tanaka-su951/mtk64ebt/image/fooswitch_bt_module.png

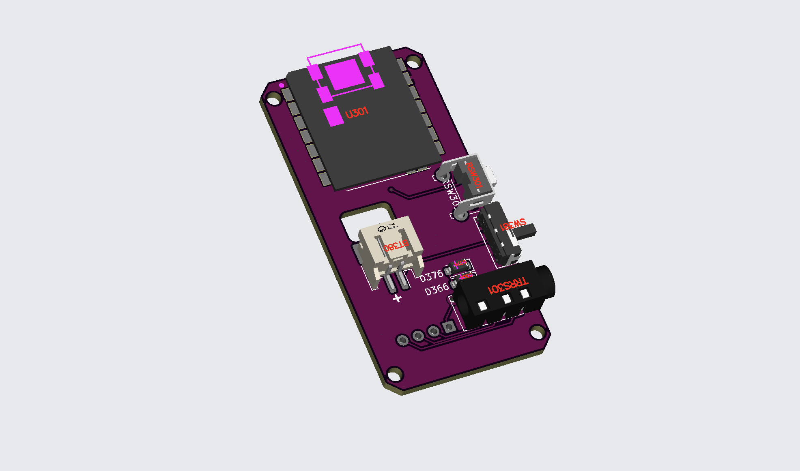
image/fooswitch_bt_module.png
