tanaka-su951/mtk64ebt/image/footmodule_gerber.png

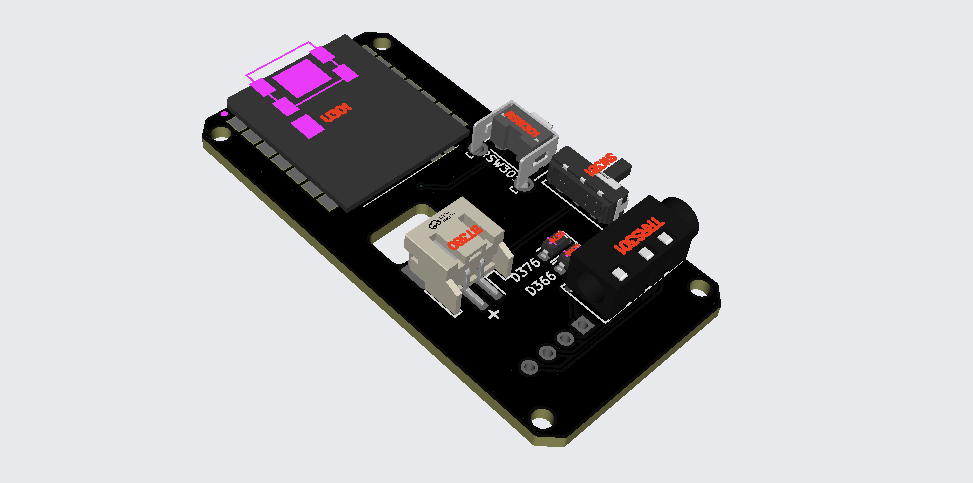
image/footmodule_gerber.png
