tanaka-su951/mtk64ebt/image/mtk64ebt_case.jpg

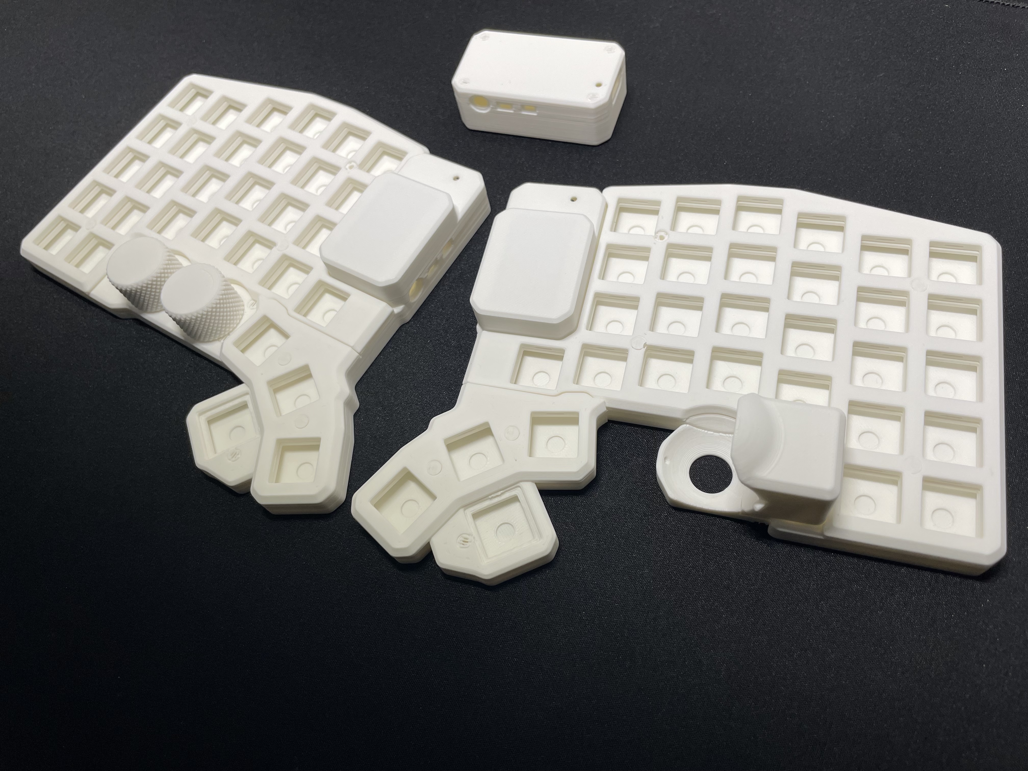
image/mtk64ebt_case.jpg
