tanaka-su951/mtk64ebt/image/mtk64ebt_L2.jpg

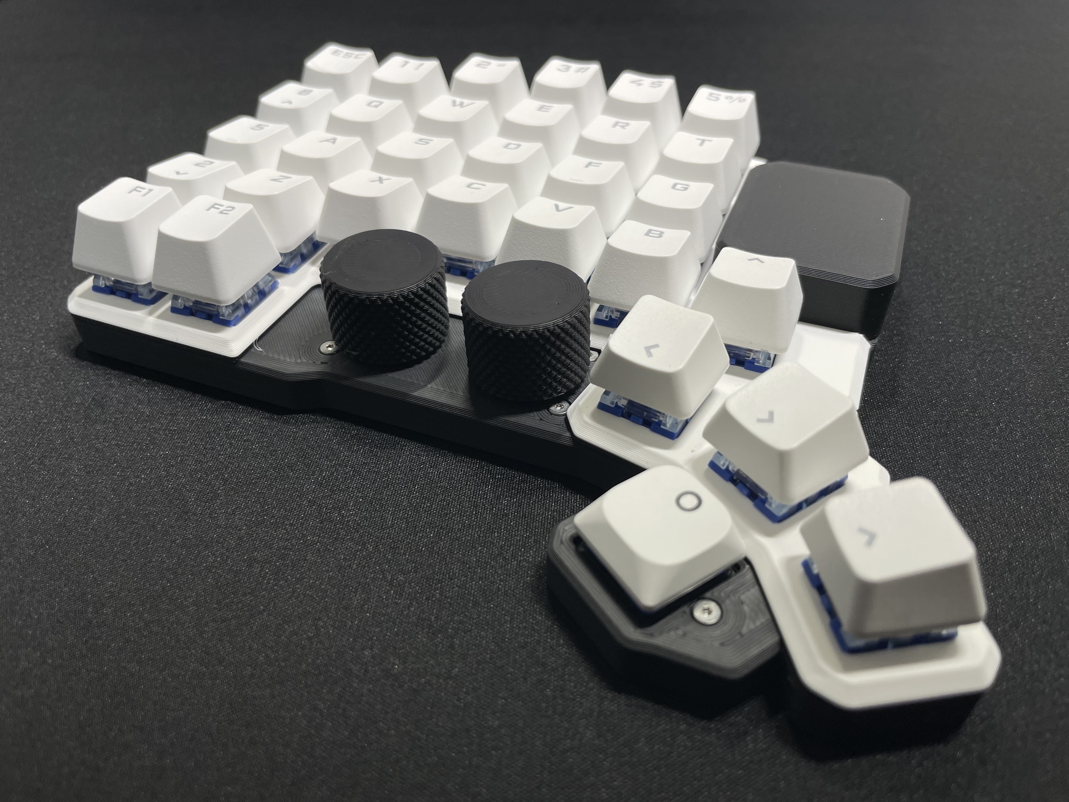
image/mtk64ebt_L2.jpg
