tanaka-su951/mtk64ebt/image/mtk64ebt_L.jpg

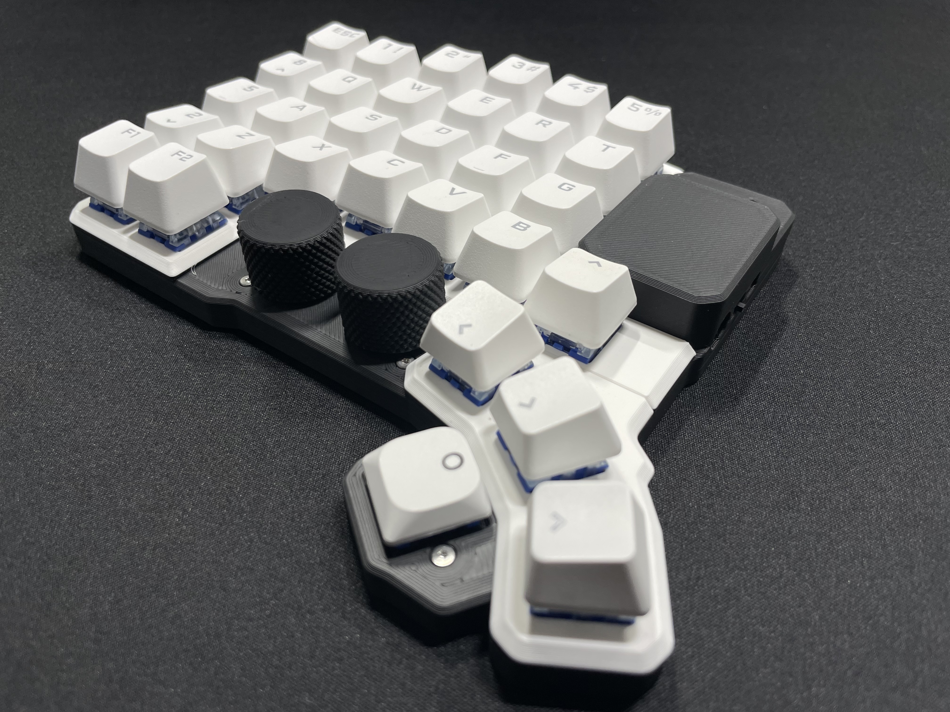
image/mtk64ebt_L.jpg
