tanaka-su951/mtk64ebt/image/mtk64ebt_lowpro.jpg

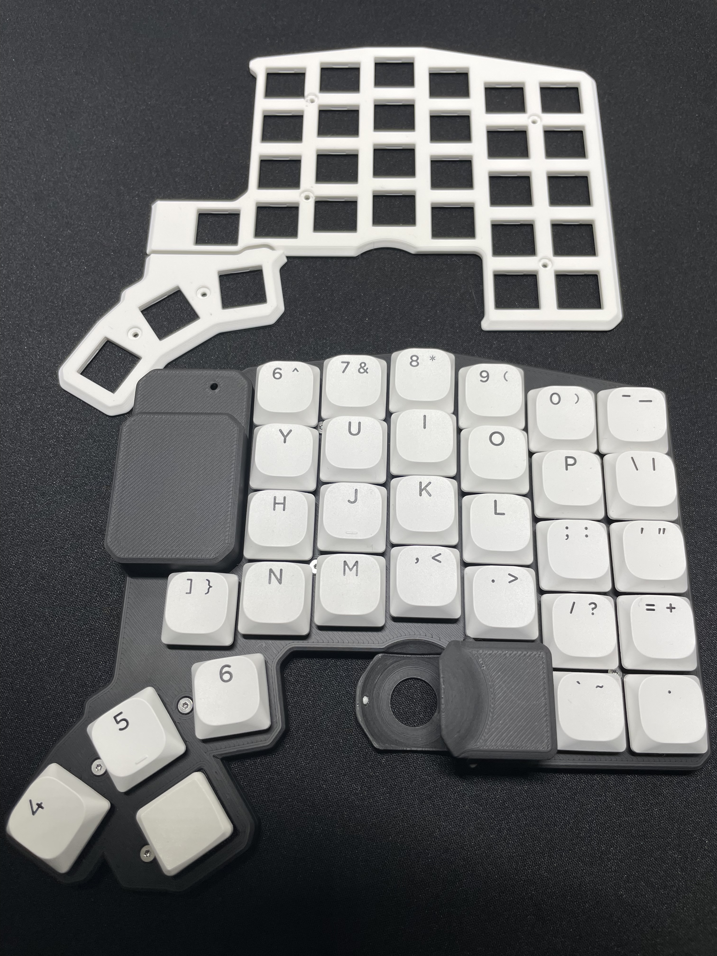
image/mtk64ebt_lowpro.jpg
