tanaka-su951/mtk64ebt/image/mtk64ebt_prototype.JPG

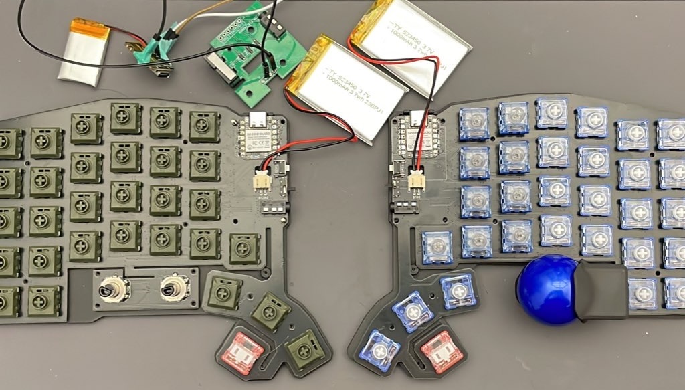
image/mtk64ebt_prototype.JPG
