tanaka-su951/mtk64ebt/image/mtk64ebt_R.jpg

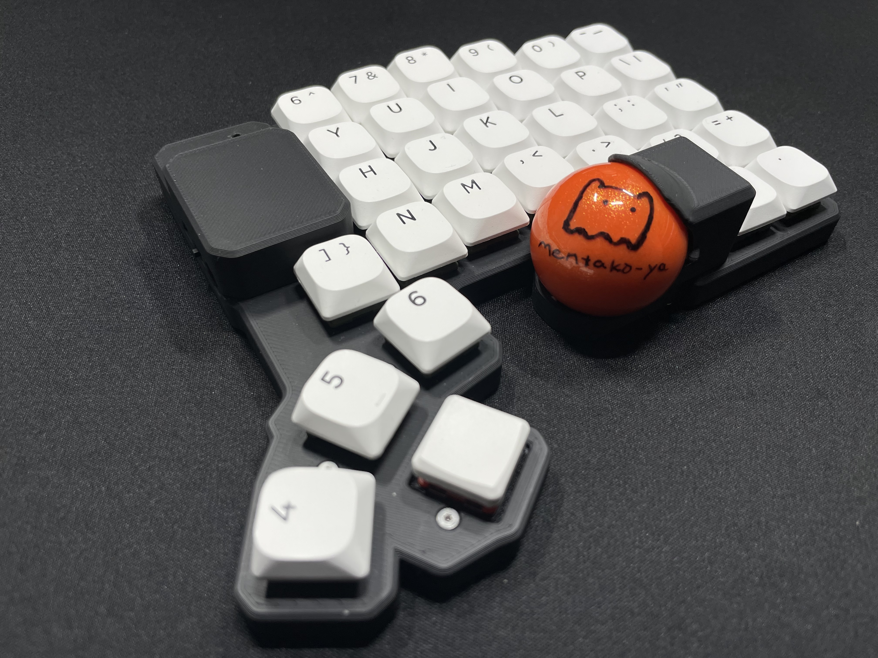
image/mtk64ebt_R.jpg
