tanaka-su951/mtk64ebt/image/mtk64ebt_switch.jpg

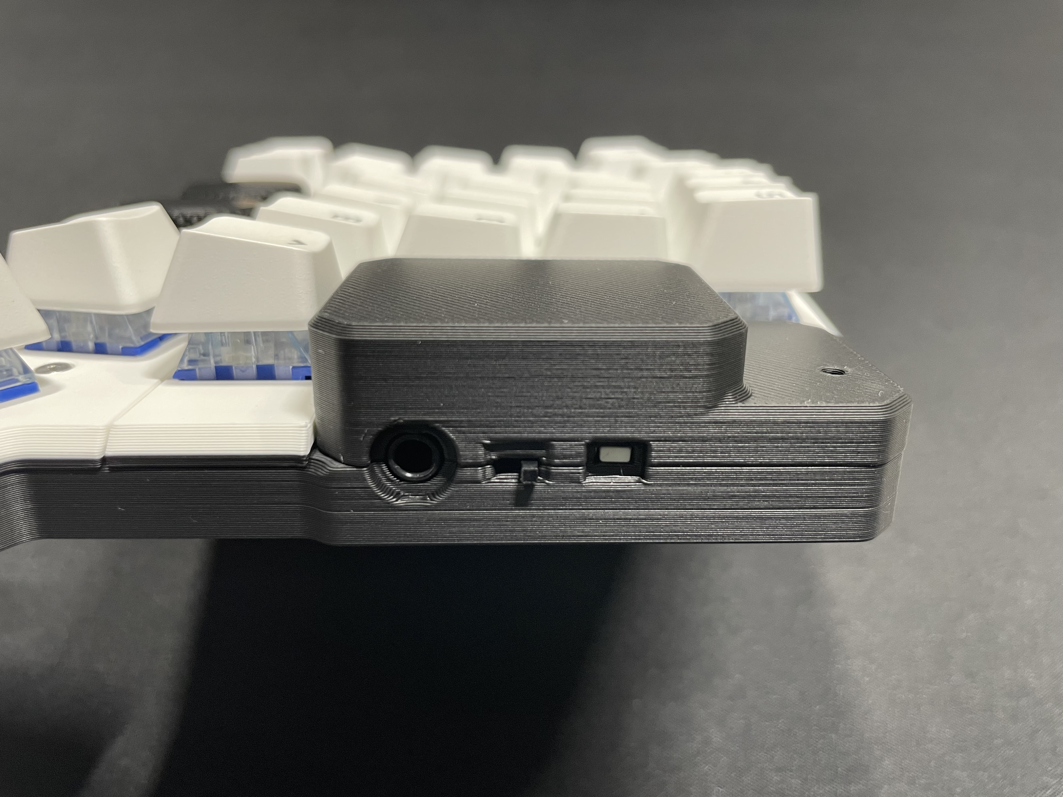
image/mtk64ebt_switch.jpg
