tanaka-su951/mtk64ebt/image/mtk64erp_footswitch_7.jpg

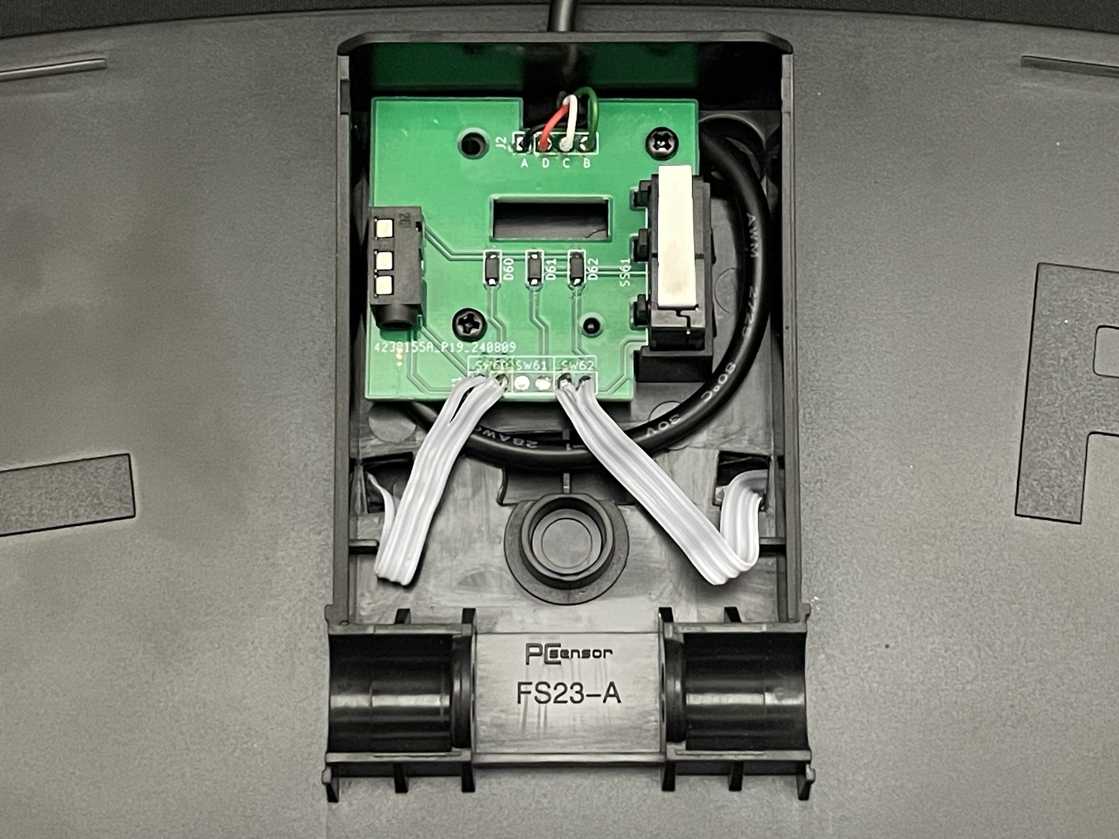
image/mtk64erp_footswitch_7.jpg
