tanaka-su951/mtk64ebt/image/rev3/7.footswitch.jpg

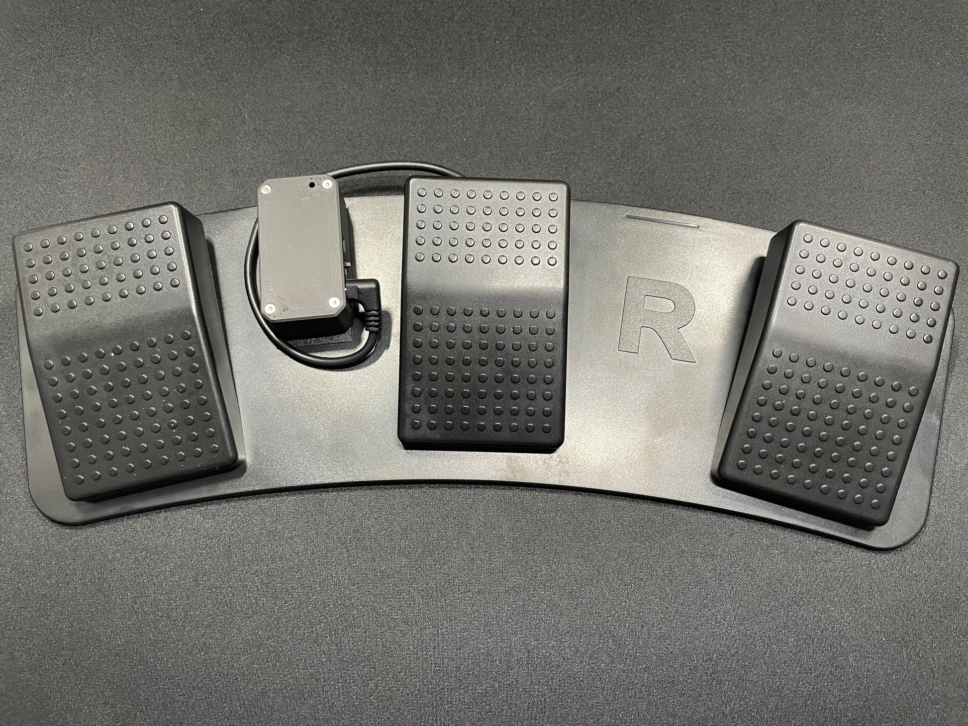
image/rev3/7.footswitch.jpg
