tanaka-su951/mtk64ebt/image/rev3/8.footswitch_extend.jpg

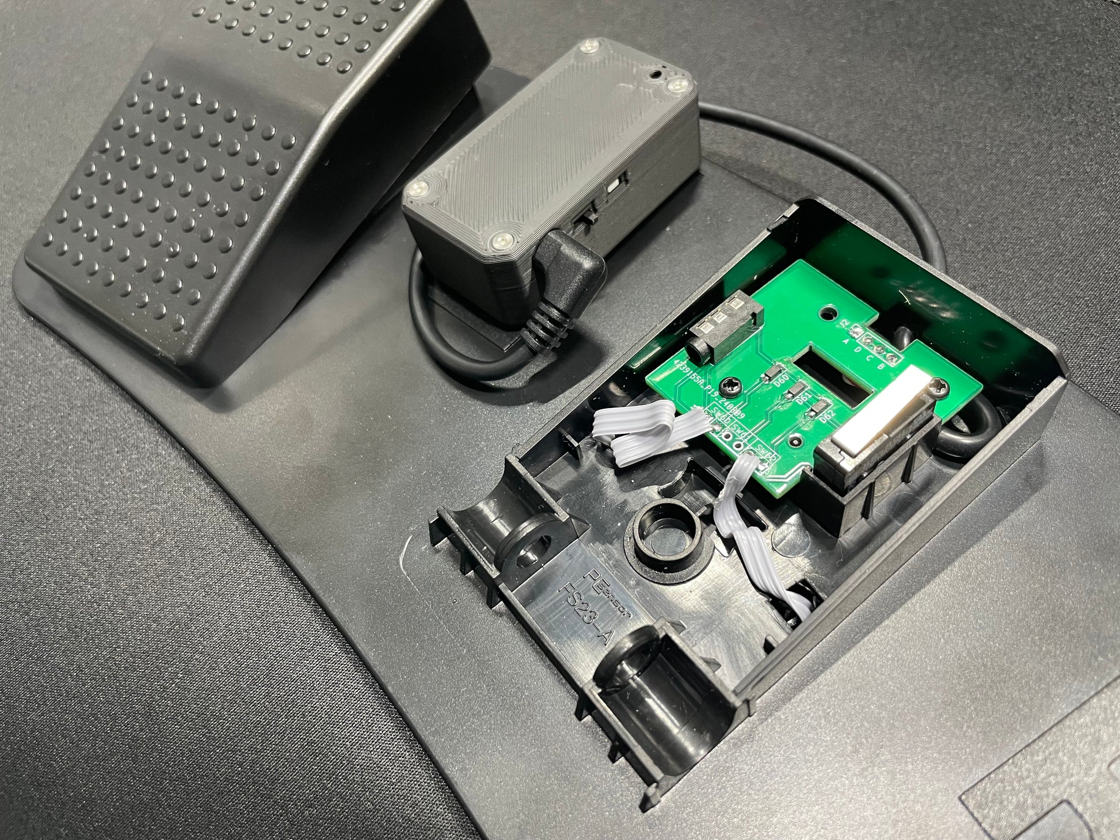
image/rev3/8.footswitch_extend.jpg
