tanaka-su951/mtk64ebt/image/rev3/mtk64ebt_rev3_black.JPG

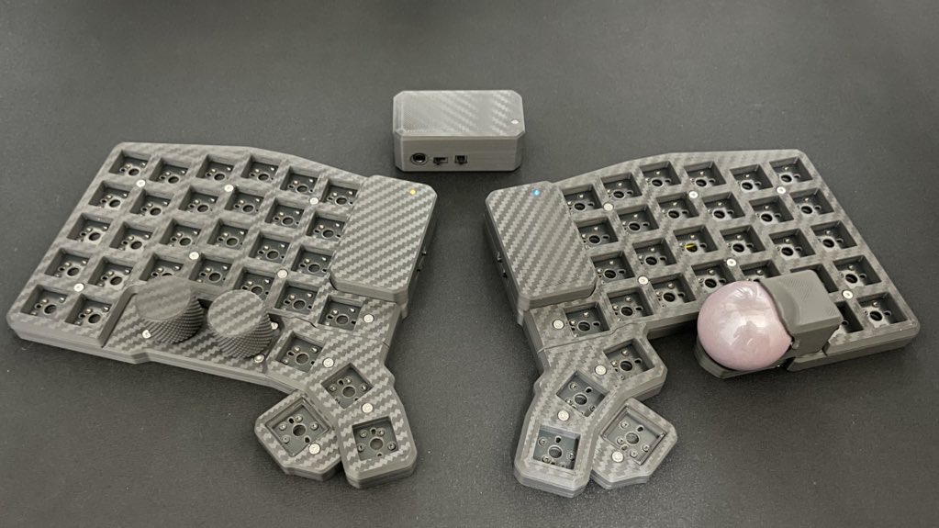
image/rev3/mtk64ebt_rev3_black.JPG
