tanaka-su951/mtk64ebt/image/rev3/mtk64ebt_rev3_trace.png

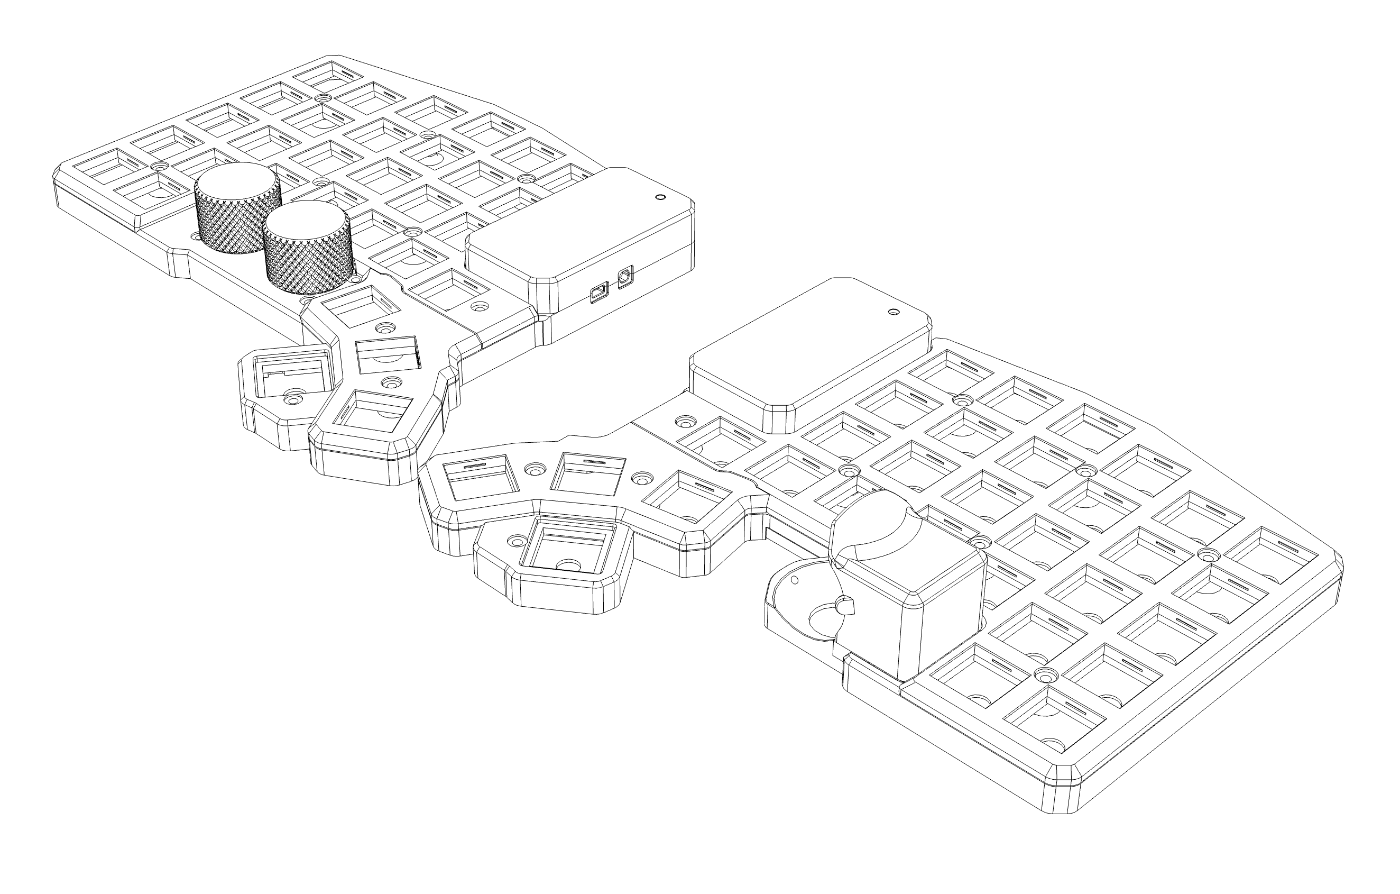
image/rev3/mtk64ebt_rev3_trace.png
