tanaka-su951/mtk64ebt/casedata/rev2/mtk64ebt_rev2_ballcase_off10_deg10_RH.3mf

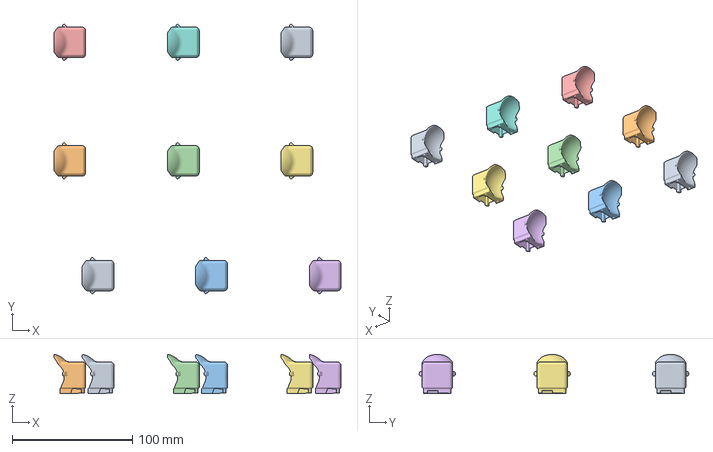
[picture p68: CAD file, 2025-07-19, an earlier design]
casedata/rev2/mtk64ebt_rev2_ballcase_off10_deg10_RH.3mf
238.7 x 224.2 x 32.5 mm
mtk64ebt_rev2_ballcase_off10_deg10_LH x 9
